SolderedElectronics/Dasduino-CORE-hardware-design/OUTPUTS/V1.1.1/333037 (2).jpg

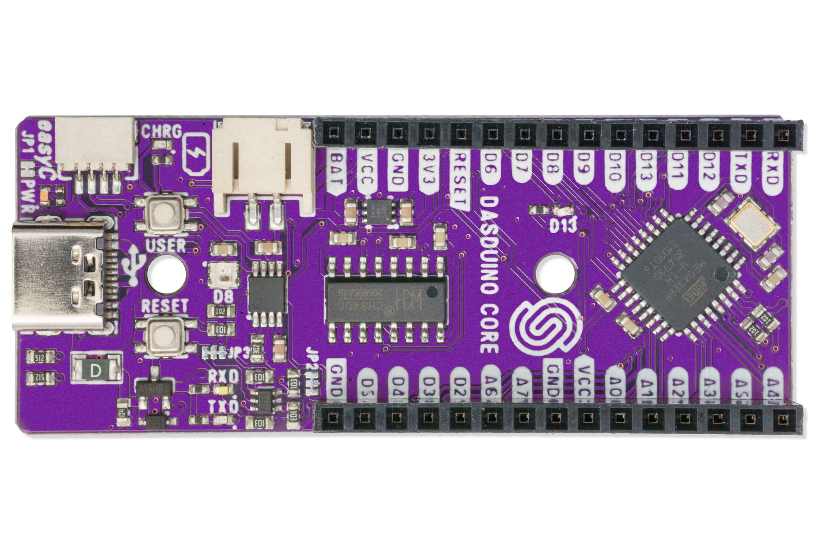
OUTPUTS/V1.1.1/333037 (2).jpg
