SolderedElectronics/Dasduino-CORE-hardware-design/OUTPUTS/V1.1.1/Dasduino CORE Pinout.jpg

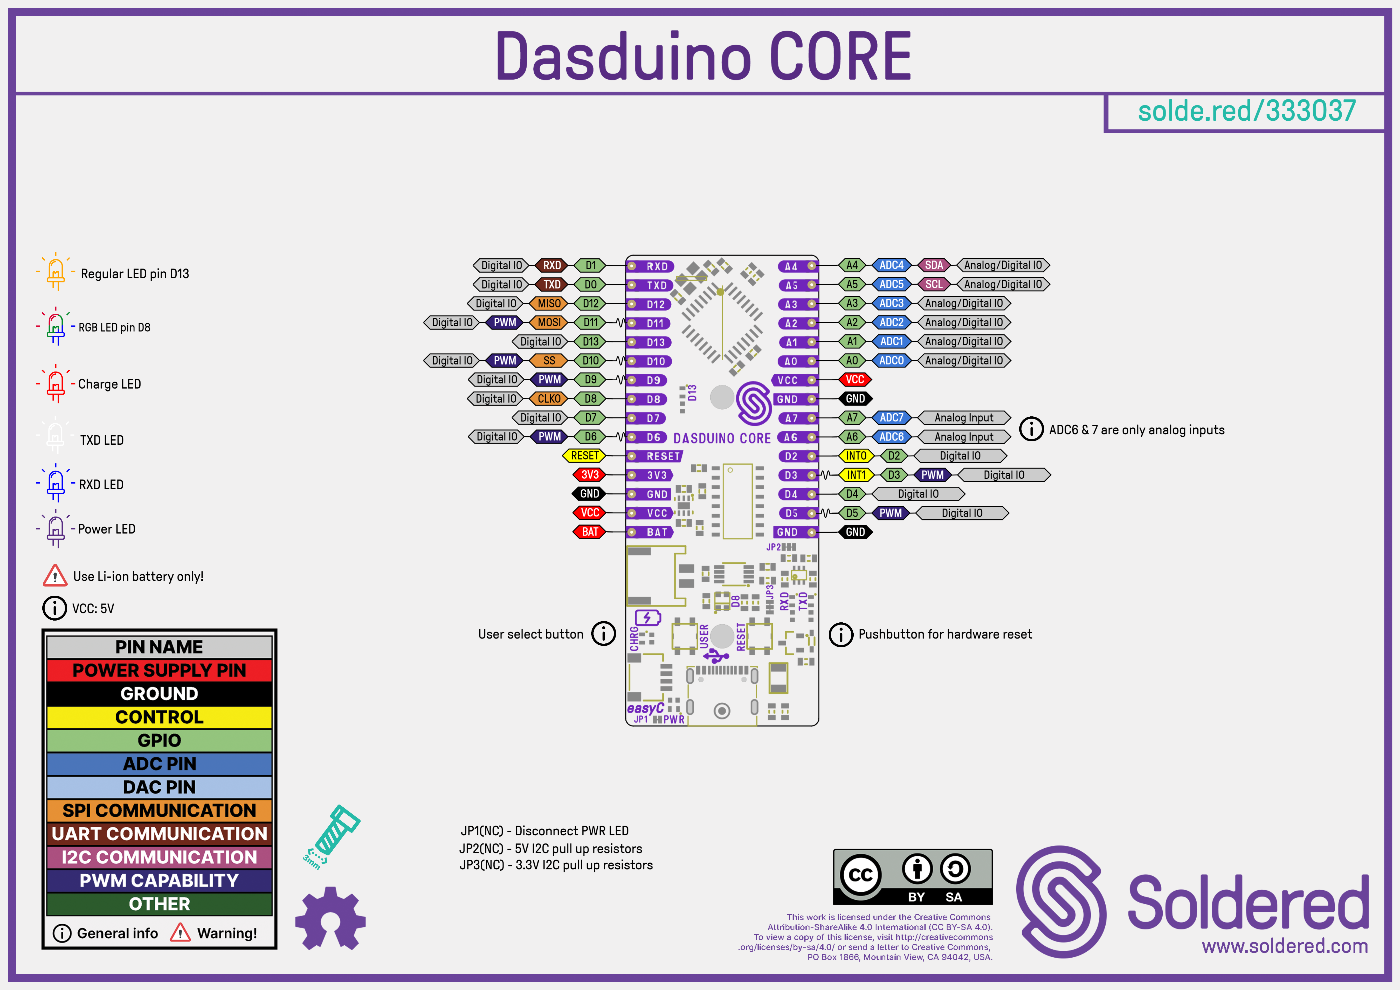
OUTPUTS/V1.1.1/Dasduino CORE Pinout.jpg
